darknoon/tunepower/readme-media/Digispark_front.jpg

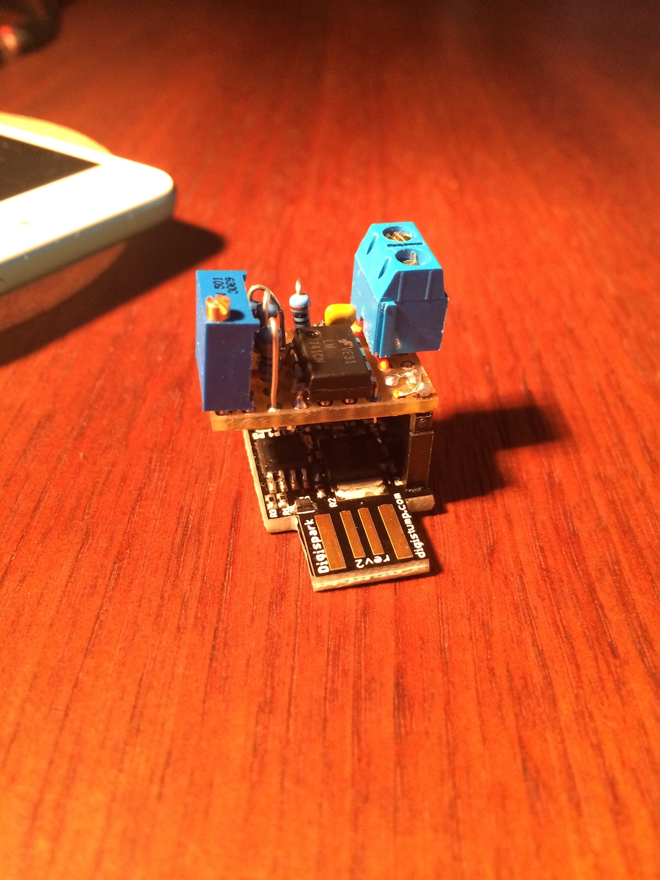
readme-media/Digispark_front.jpg
